Jaknil/Dancing_lights/img/antenna_collapsed.jpg

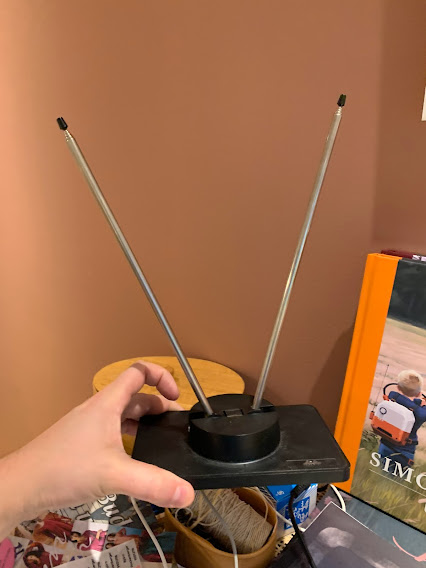
img/antenna_collapsed.jpg
