Jaknil/Dancing_lights/img/cam_base.jpg

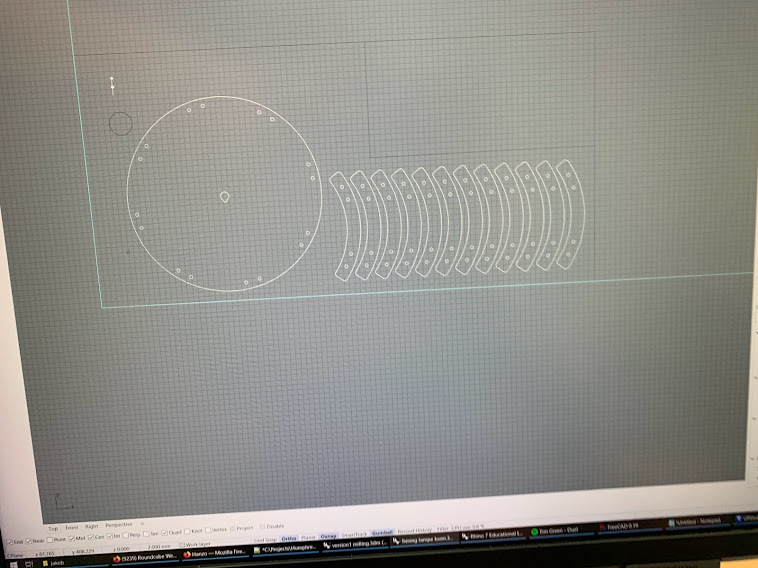
img/cam_base.jpg
