Jaknil/Dancing_lights/img/clamping_base.jpg

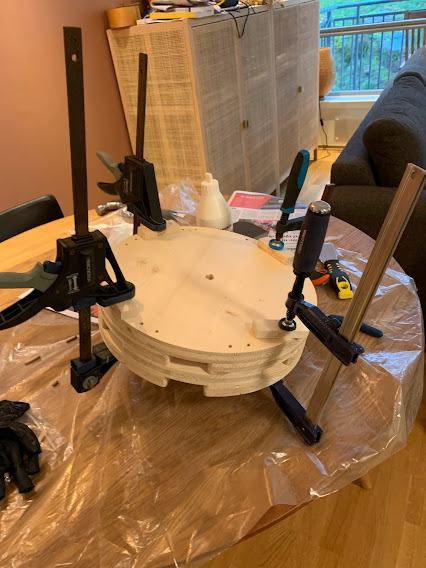
img/clamping_base.jpg
