Jaknil/Dancing_lights/img/fire.jpg

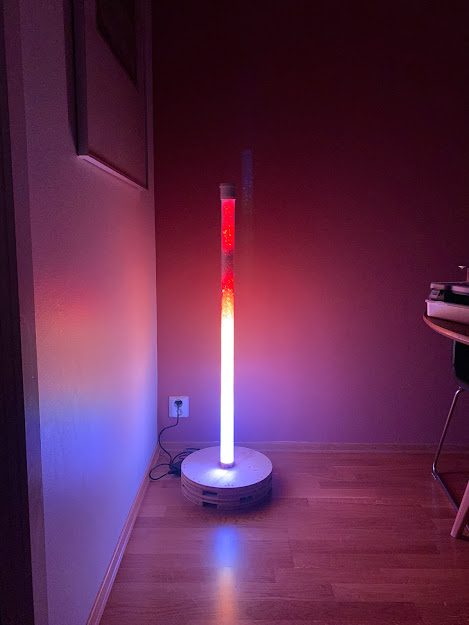
img/fire.jpg
