Jaknil/Dancing_lights/img/off.jpg

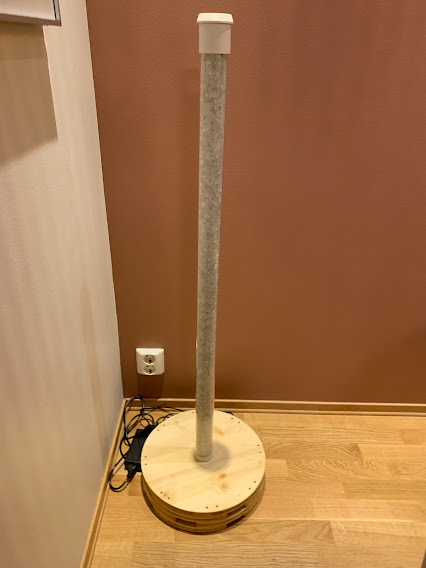
img/off.jpg
