Jaknil/Dancing_lights/img/power_flowchart.jpg

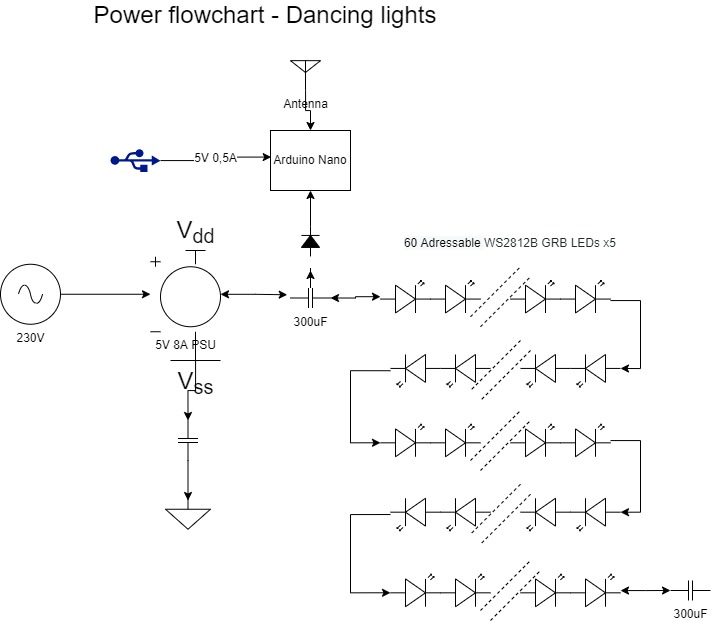
img/power_flowchart.jpg
