Jaknil/Dancing_lights/img/youtube_short.jpg

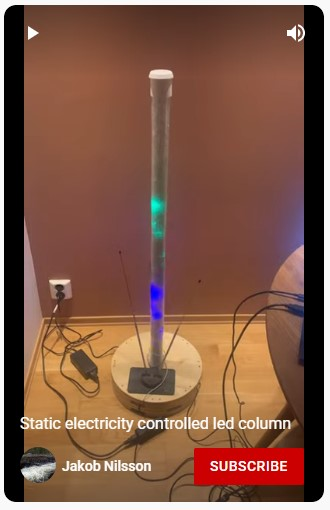
img/youtube_short.jpg
